BETOXL/P-Keeper/Plans3Dfiles/P-Keeper Plans/lateral de motor - Sheet1.pdf

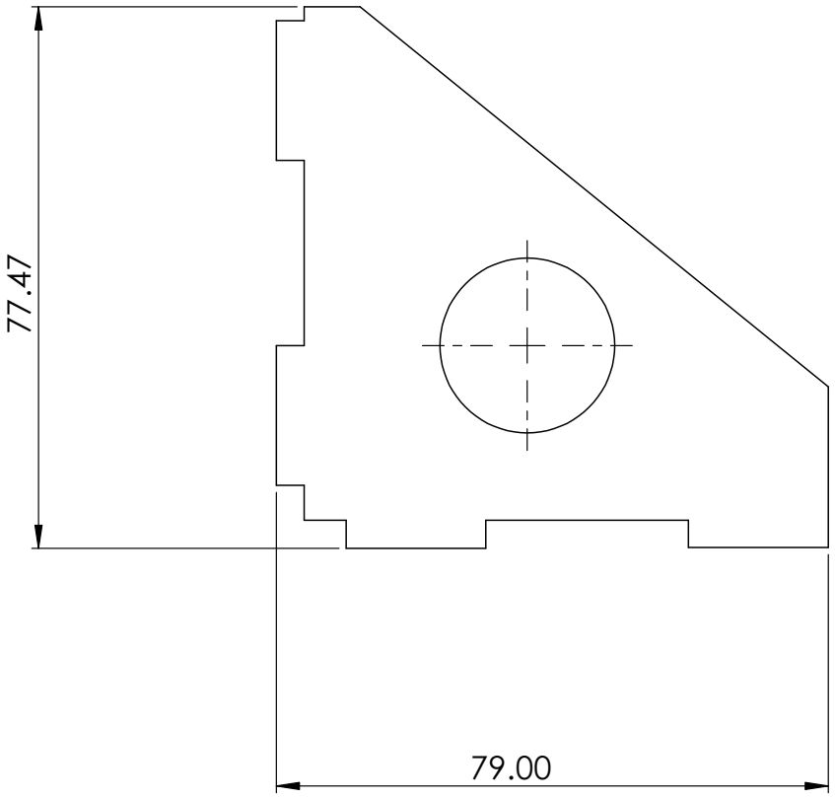
[picture p3: figure]
