BETOXL/P-Keeper/Plans3Dfiles/P-Keeper Plans/soporte de entrepiso - Sheet1.pdf

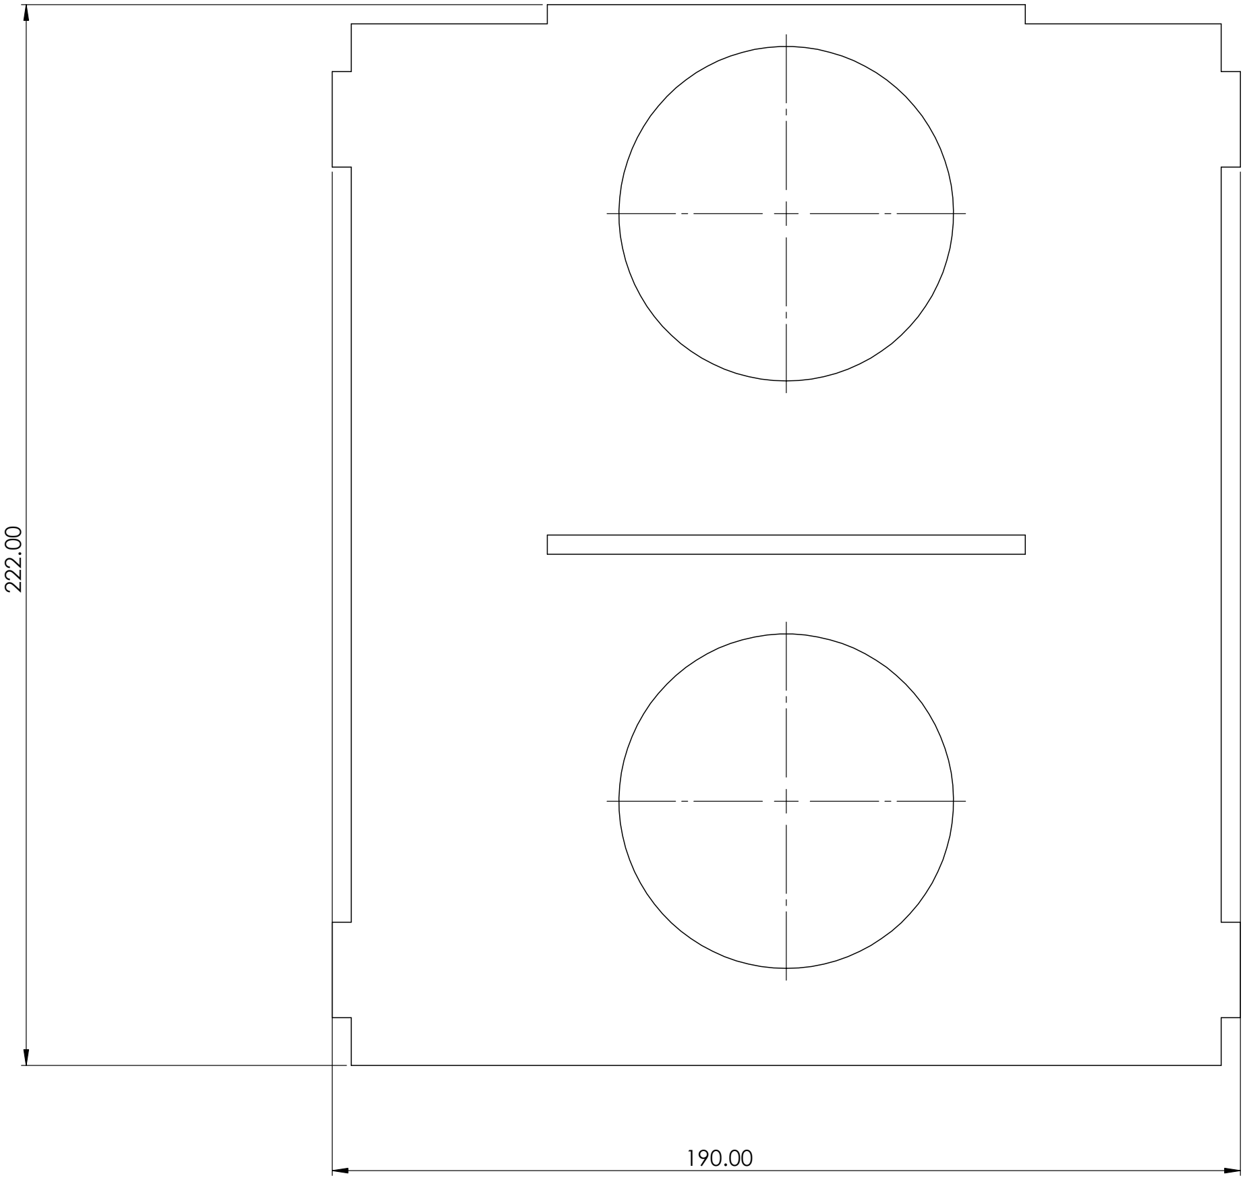
[picture p4: figure]
