BETOXL/P-Keeper/Plans3Dfiles/back.JPG

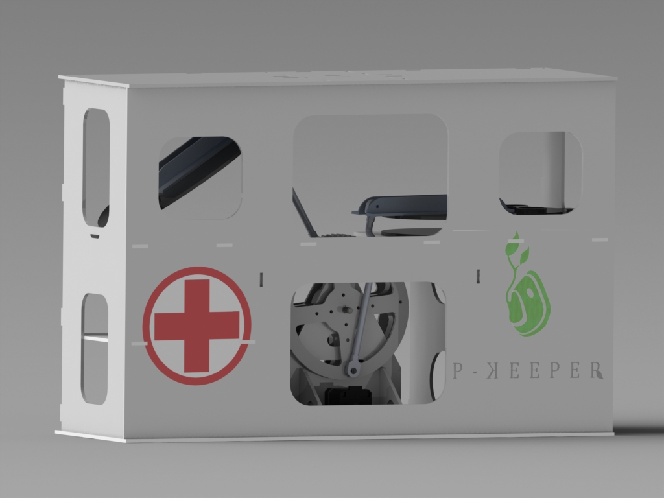
Plans3Dfiles/back.JPG
