BETOXL/P-Keeper/Plans3Dfiles/total assy.SLDASM

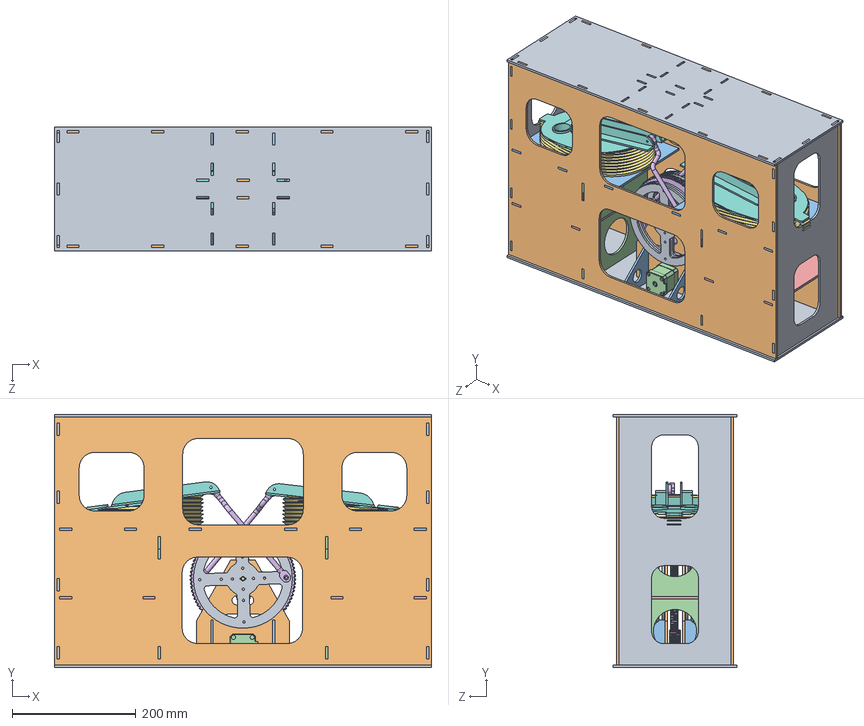
[picture p26: CAD file, 2020-05-05]
Plans3Dfiles/total assy.SLDASM
610.0 x 410.0 x 200.0 mm
piso 2 x 2
frente de motor x 2
lateral de motor x 4
nema 17 x 2
pinon
Corona
eje principal
perno de eje
rueda x 4
lateral x 2
entrepiso x 2
soporte de entrepiso x 2
piso para electronica x 2
bastago x 2
tapa de fuelle2 x 2
tapa sup de fuelle x 2
frentes x 2
