BETOXL/P-Keeper/Plans3Dfiles/Respirator2.SLDASM

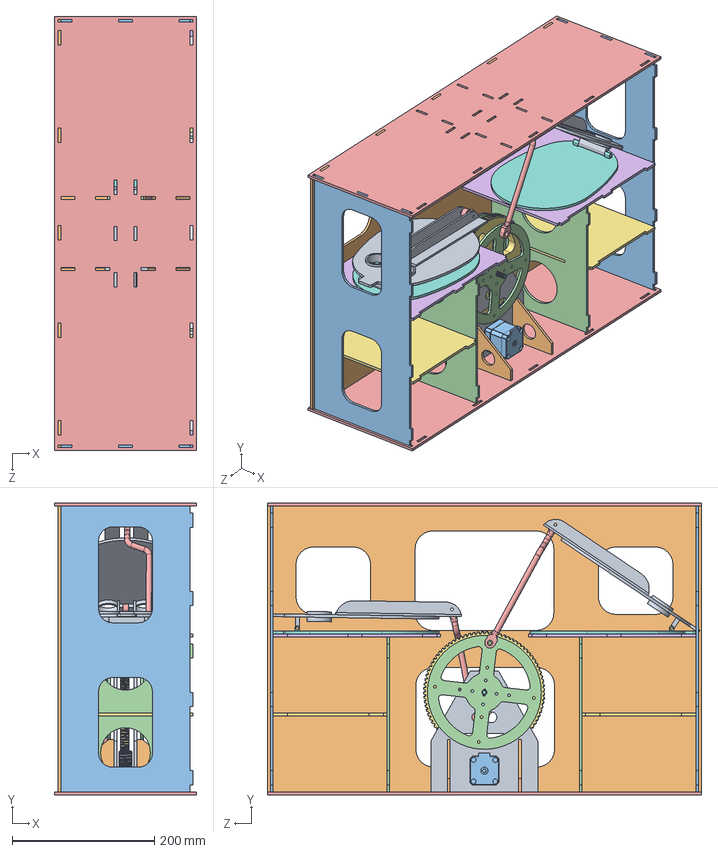
[picture p27: CAD file, 2020-05-05]
Plans3Dfiles/Respirator2.SLDASM
200.0 x 410.0 x 610.0 mm
frente de motor x 2
lateral de motor x 4
nema 17 x 2
rueda x 2
piso 2 x 2
entrepiso x 2
piso para electronica x 2
tapa de fuelle x 2
tapa sup de fuelle x 2
lateral
frentes x 2
soporte de entrepiso x 2
bastago x 2
pinon
Corona
eje principal
perno de eje x 3
