BETOXL/P-Keeper/Plans3Dfiles/main gear 94t.SLDPRT

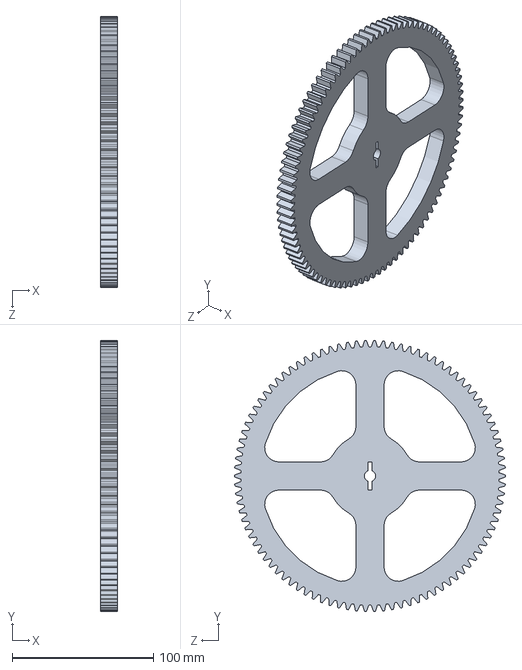
[picture p28: CAD file, 2020-05-05]
Plans3Dfiles/main gear 94t.SLDPRT
12.0 x 191.9 x 192.0 mm
