BETOXL/P-Keeper/Plans3Dfiles/3D files P-Keeper/niple conector de manguera.STL

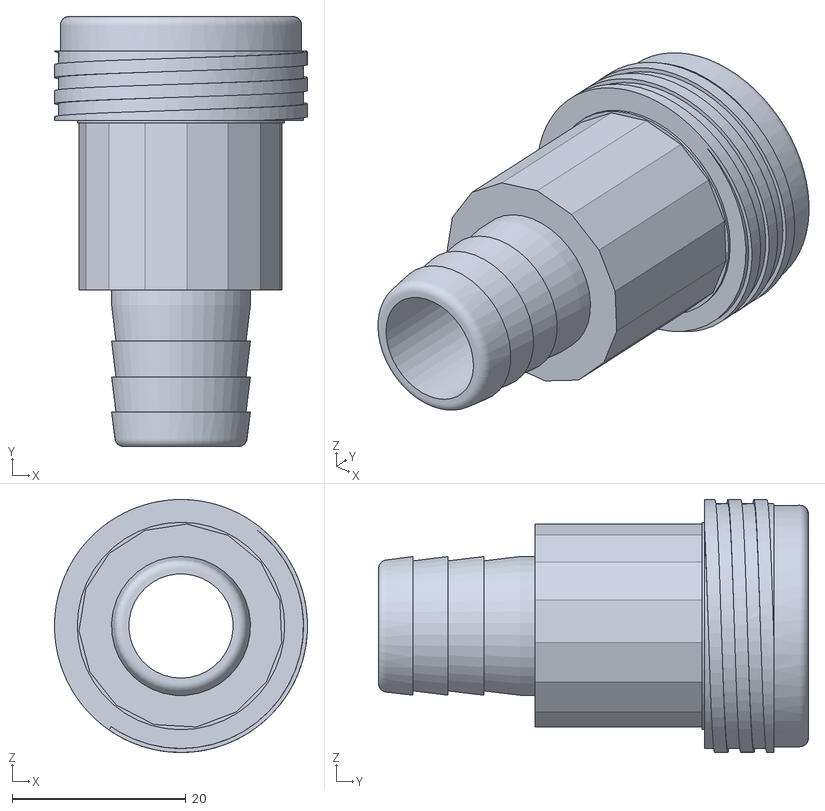
[picture p29: CAD file, 2020-05-05]
Plans3Dfiles/3D files P-Keeper/niple conector de manguera.STL
29.1 x 49.5 x 29.1
