BETOXL/P-Keeper/Plans3Dfiles/tapa sup de fuelle.SLDPRT

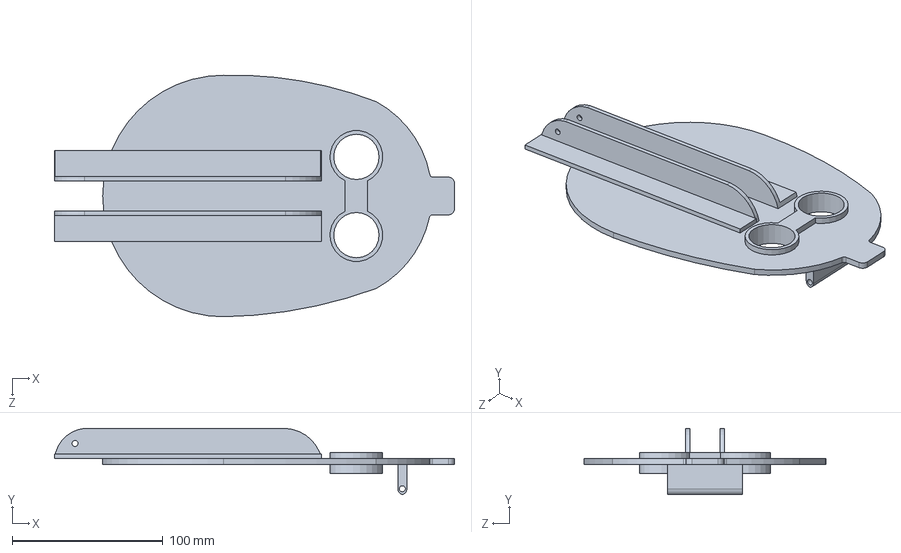
[picture p30: CAD file, 2020-05-05]
Plans3Dfiles/tapa sup de fuelle.SLDPRT
265.0 x 43.9 x 160.0 mm
