BETOXL/P-Keeper/Plans3Dfiles/3D files P-Keeper/tuerca de camara Y.STL

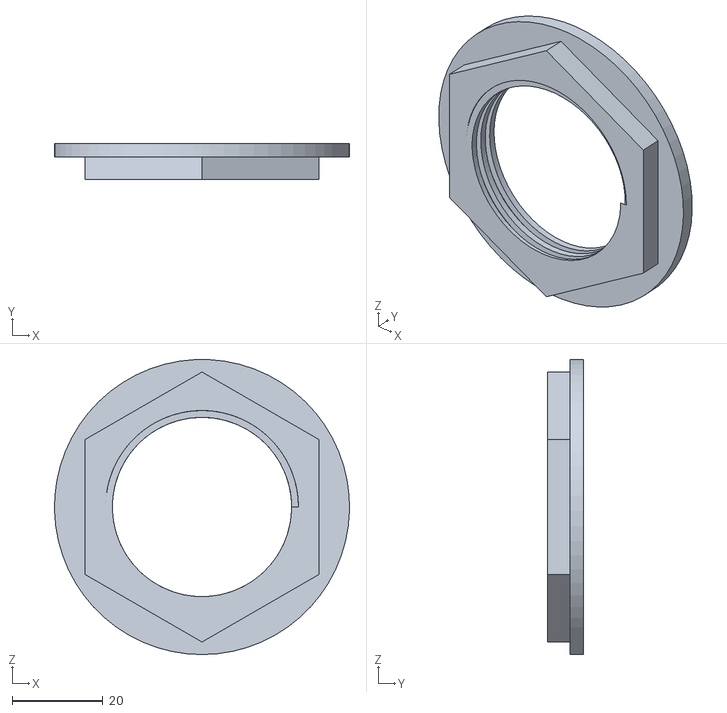
[picture p31: CAD file, 2020-05-05]
Plans3Dfiles/3D files P-Keeper/tuerca de camara Y.STL
65.0 x 8.00 x 65.0
