BETOXL/P-Keeper/Plans3Dfiles/potenciometer top.SLDPRT

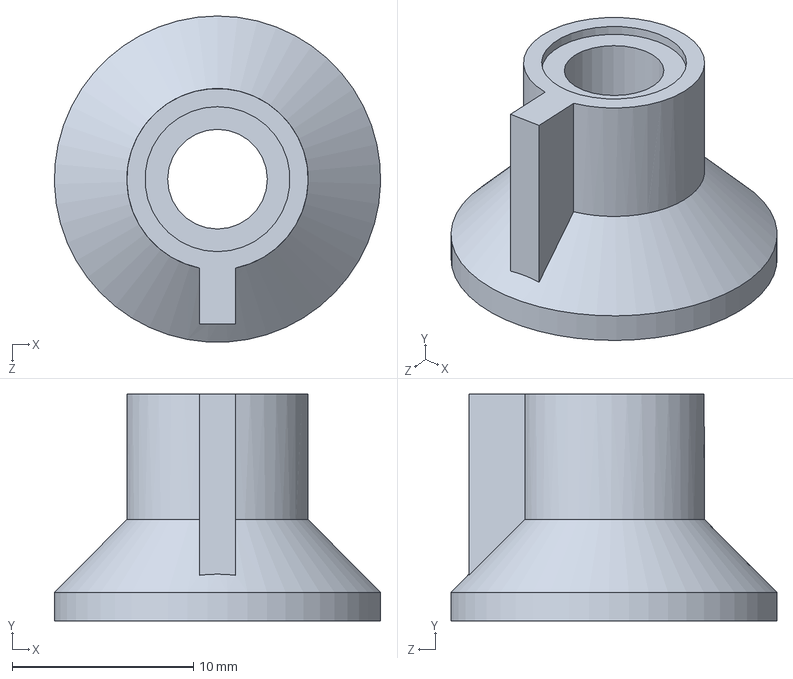
[picture p32: CAD file, 2020-05-05]
Plans3Dfiles/potenciometer top.SLDPRT
18.0 x 12.5 x 18.0 mm
