BETOXL/P-Keeper/Plans3Dfiles/3D files P-Keeper/boquilla con tuerca.STL

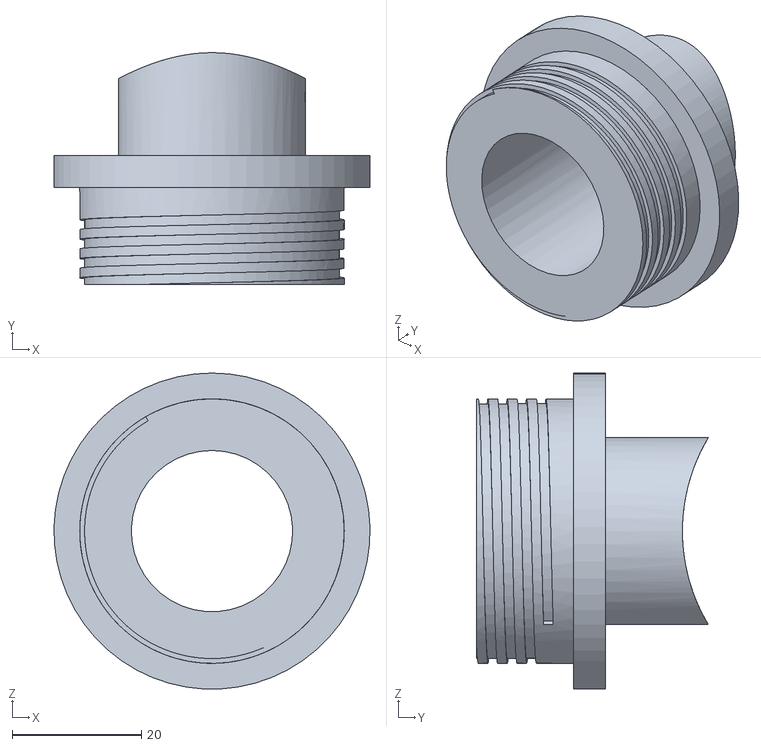
[picture p33: CAD file, 2020-05-05]
Plans3Dfiles/3D files P-Keeper/boquilla con tuerca.STL
49.0 x 35.9 x 49.0
