BETOXL/P-Keeper/Plans3Dfiles/Secondary Gear 3.SLDPRT

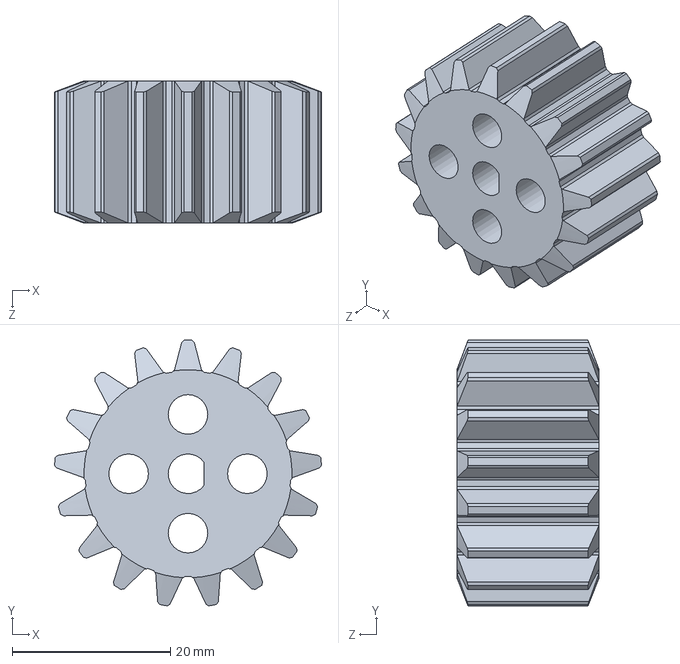
[picture p34: CAD file, 2020-05-05]
Plans3Dfiles/Secondary Gear 3.SLDPRT
33.7 x 33.6 x 18.0 mm
