BETOXL/P-Keeper/Plans3Dfiles/3D files P-Keeper/tapa de camara.STL

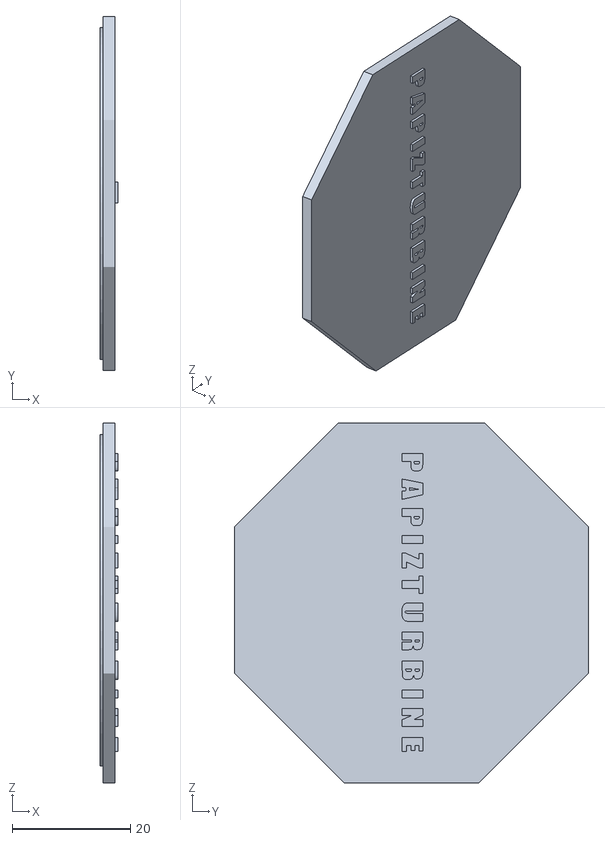
[picture p35: CAD file, 2020-05-05]
Plans3Dfiles/3D files P-Keeper/tapa de camara.STL
3.00 x 60.0 x 61.0
