BETOXL/P-Keeper/Plans3Dfiles/Shaft PIN.SLDPRT

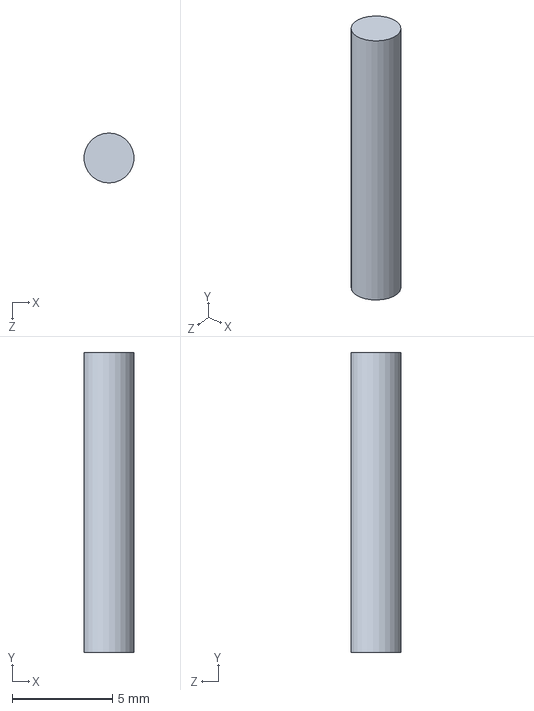
[picture p36: CAD file, 2020-05-05]
Plans3Dfiles/Shaft PIN.SLDPRT
2.48 x 15.0 x 2.50 mm
