BETOXL/P-Keeper/Plans3Dfiles/3D files P-Keeper/conector Y comun.STL

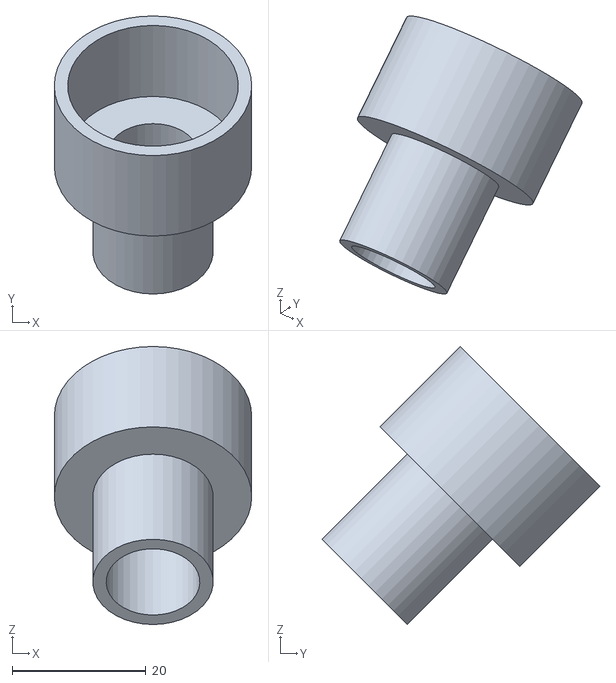
[picture p37: CAD file, 2020-05-05]
Plans3Dfiles/3D files P-Keeper/conector Y comun.STL
29.5 x 41.5 x 41.5
