BETOXL/P-Keeper/Plans3Dfiles/nema 17.SLDPRT

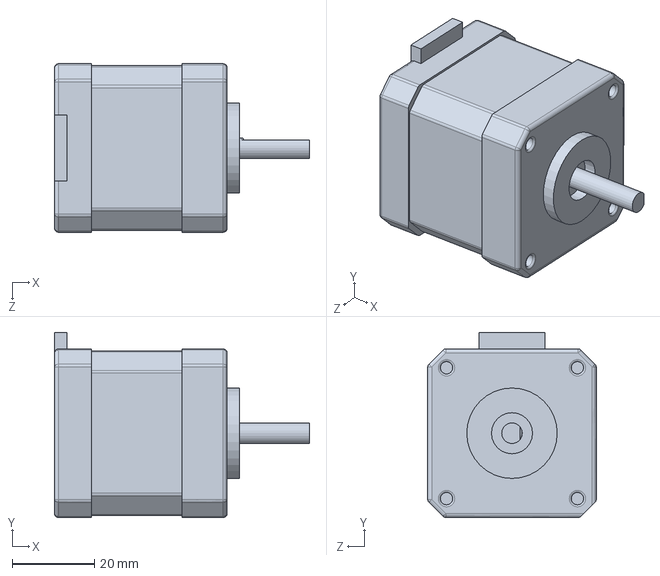
[picture p38: CAD file, 2020-05-05]
Plans3Dfiles/nema 17.SLDPRT
62.0 x 45.0 x 41.0 mm
