BETOXL/P-Keeper/Plans3Dfiles/3D files P-Keeper/cuerpo de Camara Y.STL

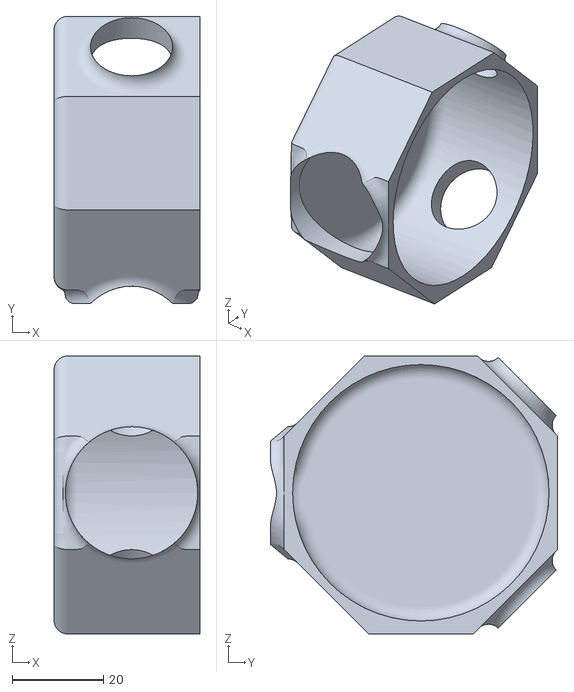
[picture p39: CAD file, 2020-05-05]
Plans3Dfiles/3D files P-Keeper/cuerpo de Camara Y.STL
32.0 x 63.0 x 61.0
