BETOXL/P-Keeper/Plans3Dfiles/Actuator Support.STL

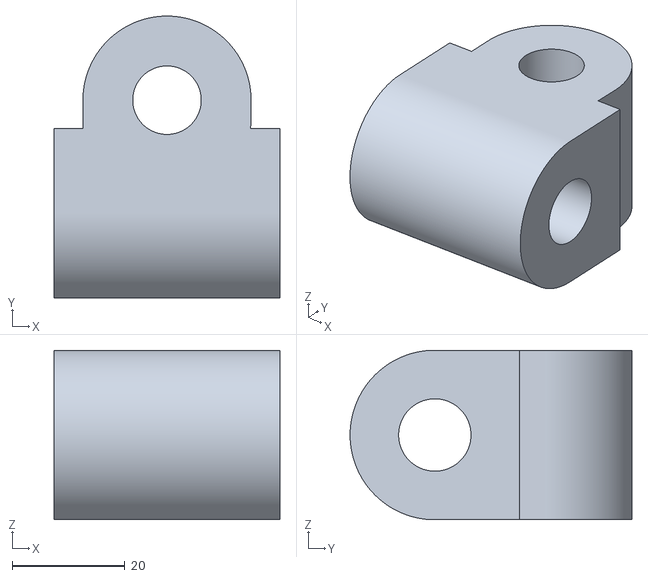
[picture p40: CAD file, 2020-05-05]
Plans3Dfiles/Actuator Support.STL
40.0 x 49.9 x 30.0
