BETOXL/P-Keeper/Plans3Dfiles/crown3.SLDPRT

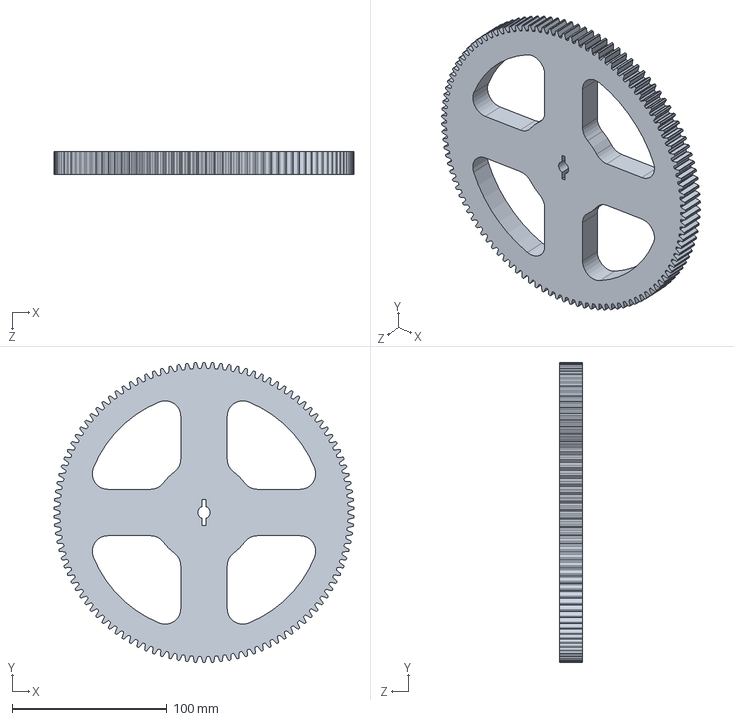
[picture p41: CAD file, 2020-05-05]
Plans3Dfiles/crown3.SLDPRT
193.7 x 193.8 x 15.0 mm
