BETOXL/P-Keeper/Plans3Dfiles/both Shafts distance.SLDPRT

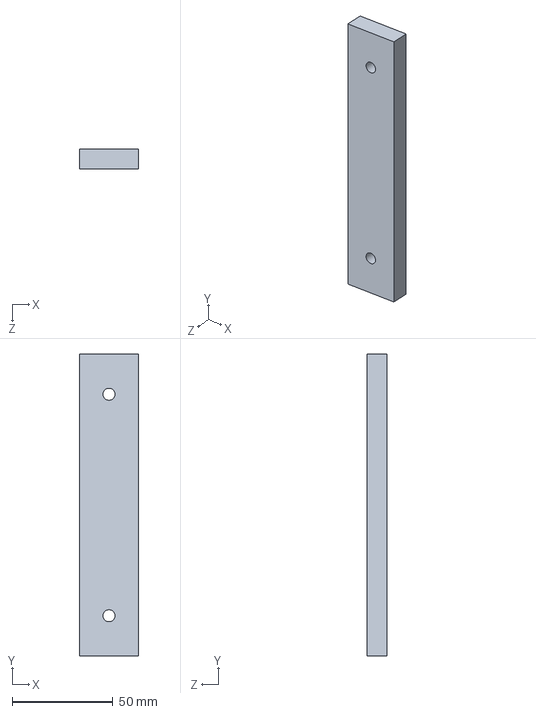
[picture p42: CAD file, 2020-05-05]
Plans3Dfiles/both Shafts distance.SLDPRT
29.2 x 150.0 x 10.0 mm
