BETOXL/P-Keeper/Plans3Dfiles/Secondary Gear.SLDPRT

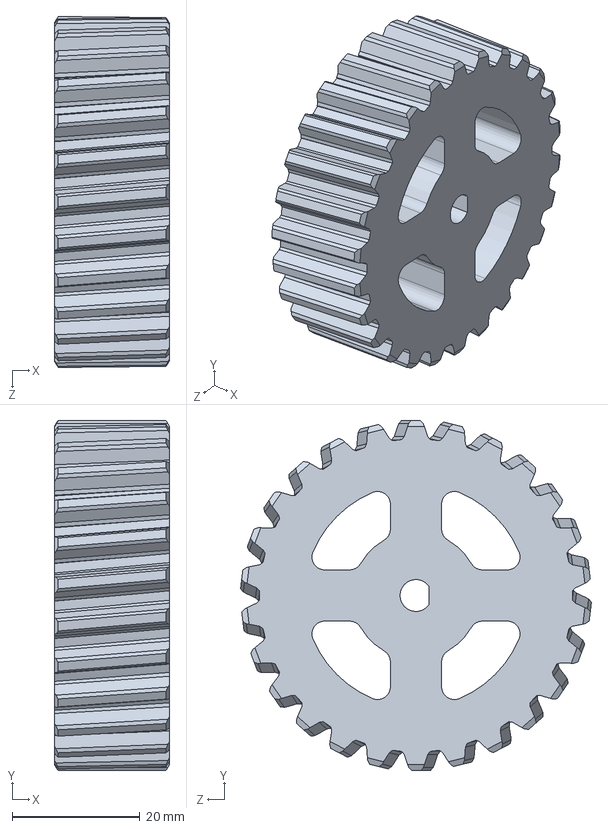
[picture p43: CAD file, 2020-05-05]
Plans3Dfiles/Secondary Gear.SLDPRT
18.0 x 54.8 x 54.9 mm
