BETOXL/P-Keeper/Plans3Dfiles/common conector.SLDPRT

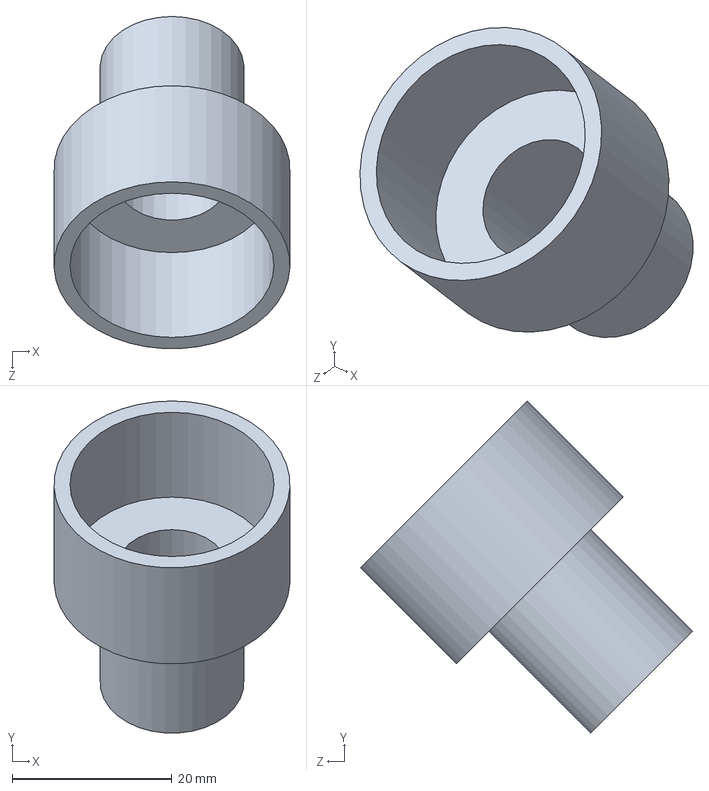
[picture p44: CAD file, 2020-05-05]
Plans3Dfiles/common conector.SLDPRT
29.5 x 41.5 x 41.5 mm
