BETOXL/P-Keeper/Plans3Dfiles/tapa de fuelle.SLDPRT

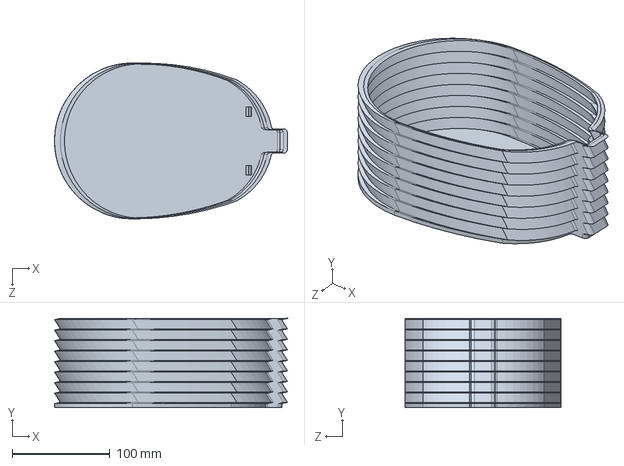
[picture p45: CAD file, 2020-05-05]
Plans3Dfiles/tapa de fuelle.SLDPRT
238.9 x 91.5 x 160.0 mm
