BETOXL/P-Keeper/Plans3Dfiles/crown 2.SLDPRT

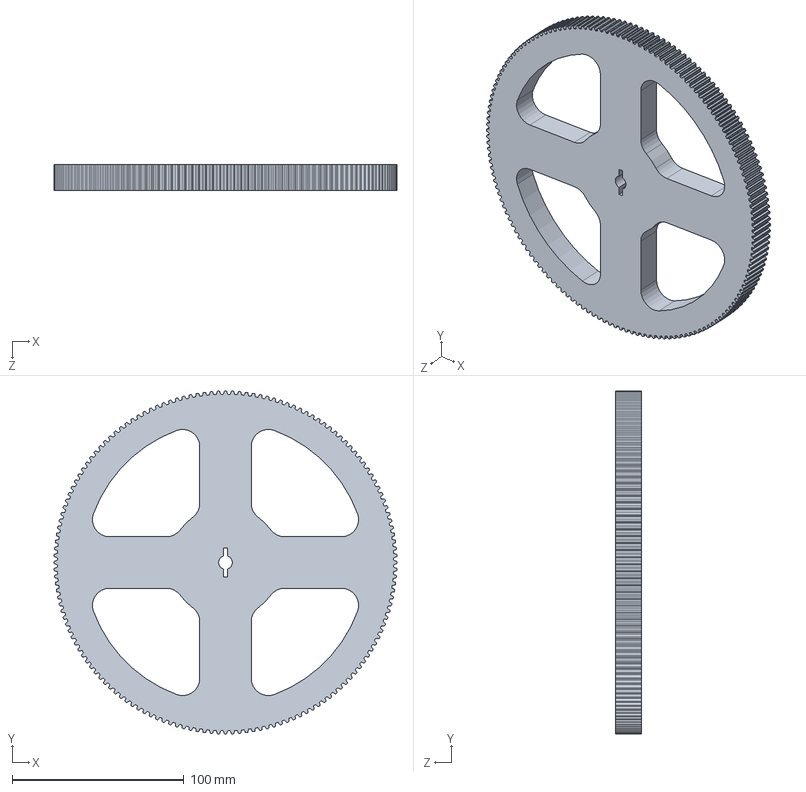
[picture p46: CAD file, 2020-05-05]
Plans3Dfiles/crown 2.SLDPRT
199.8 x 199.8 x 15.0 mm
