BETOXL/P-Keeper/Plans3Dfiles/Floor 1.SLDPRT

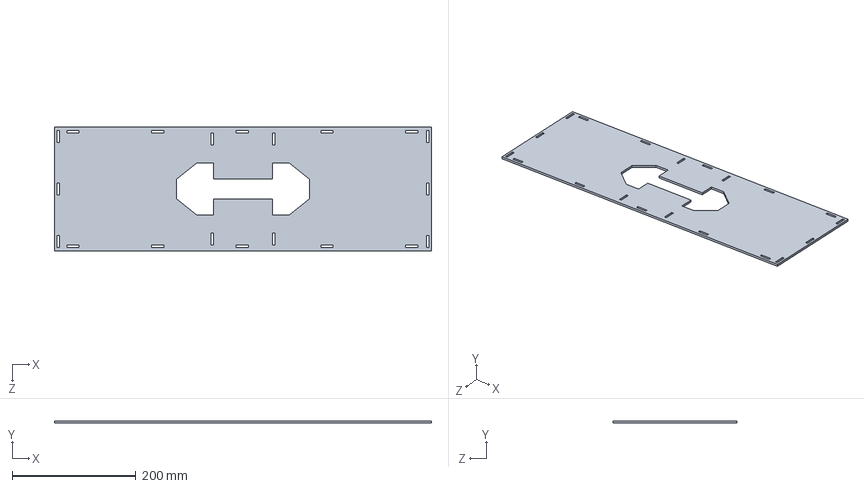
[picture p47: CAD file, 2020-05-05]
Plans3Dfiles/Floor 1.SLDPRT
610.0 x 4.00 x 200.0 mm
