BETOXL/P-Keeper/Plans3Dfiles/screen suport.SLDPRT

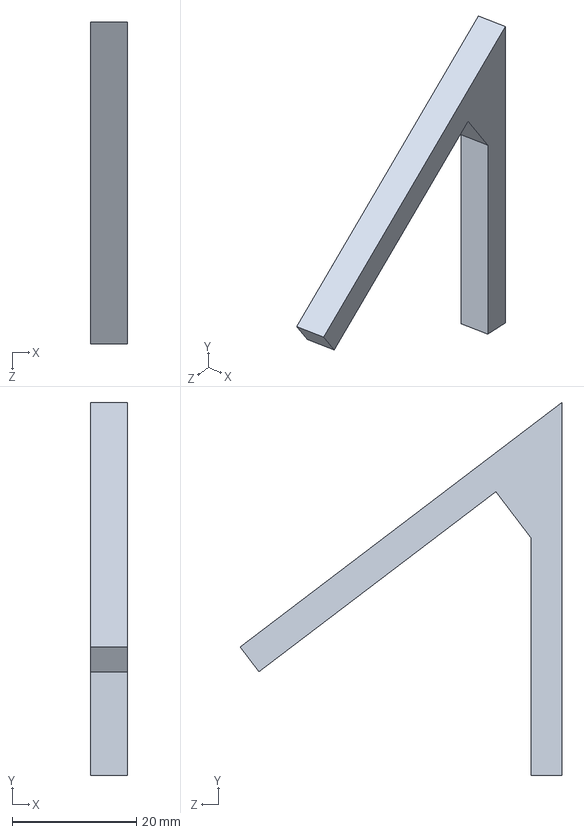
[picture p48: CAD file, 2020-05-05]
Plans3Dfiles/screen suport.SLDPRT
6.00 x 60.0 x 51.8 mm
