BETOXL/P-Keeper/Plans3Dfiles/y Chamber.SLDPRT

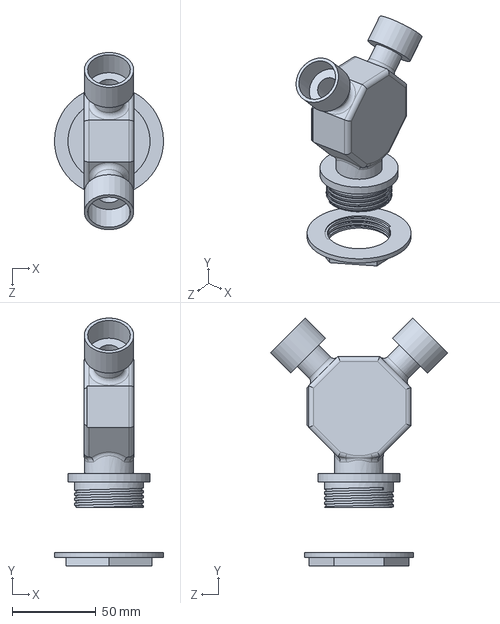
[picture p49: CAD file, 2020-05-05]
Plans3Dfiles/y Chamber.SLDPRT
65.0 x 147.9 x 105.6 mm
