BETOXL/P-Keeper/Plans3Dfiles/Actuator Wheel.SLDPRT

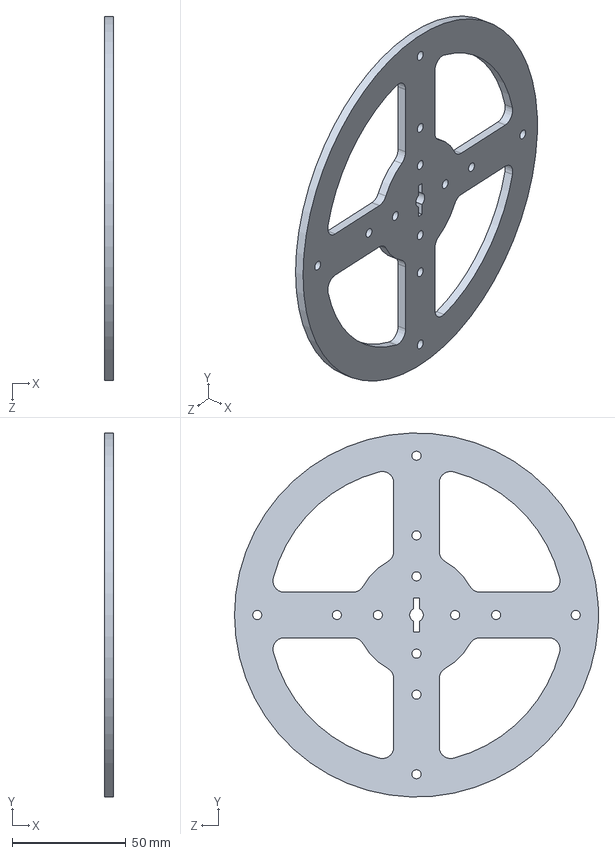
[picture p50: CAD file, 2020-05-05]
Plans3Dfiles/Actuator Wheel.SLDPRT
4.00 x 159.9 x 160.0 mm
