BETOXL/P-Keeper/Plans3Dfiles/Front and Back Wall.SLDPRT

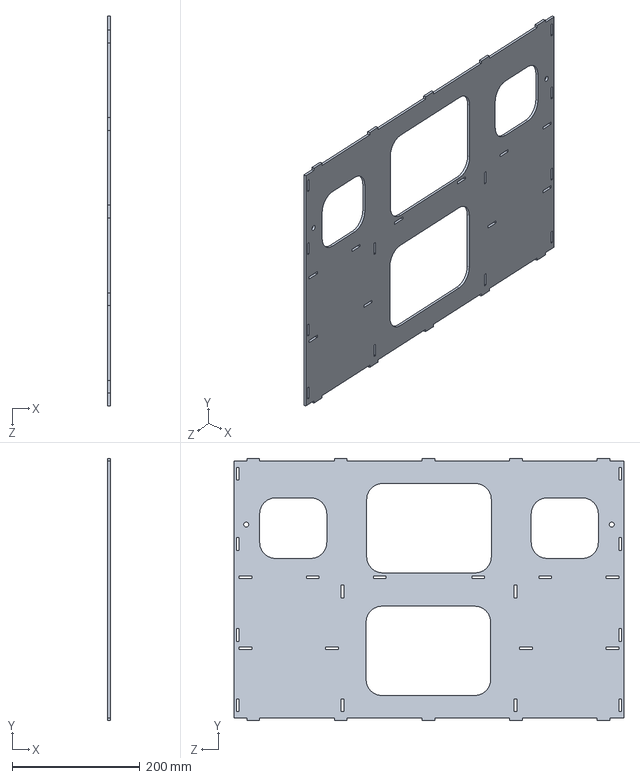
[picture p51: CAD file, 2020-05-05]
Plans3Dfiles/Front and Back Wall.SLDPRT
4.00 x 410.0 x 610.0 mm
