BETOXL/P-Keeper/Plans3Dfiles/clevis.SLDPRT

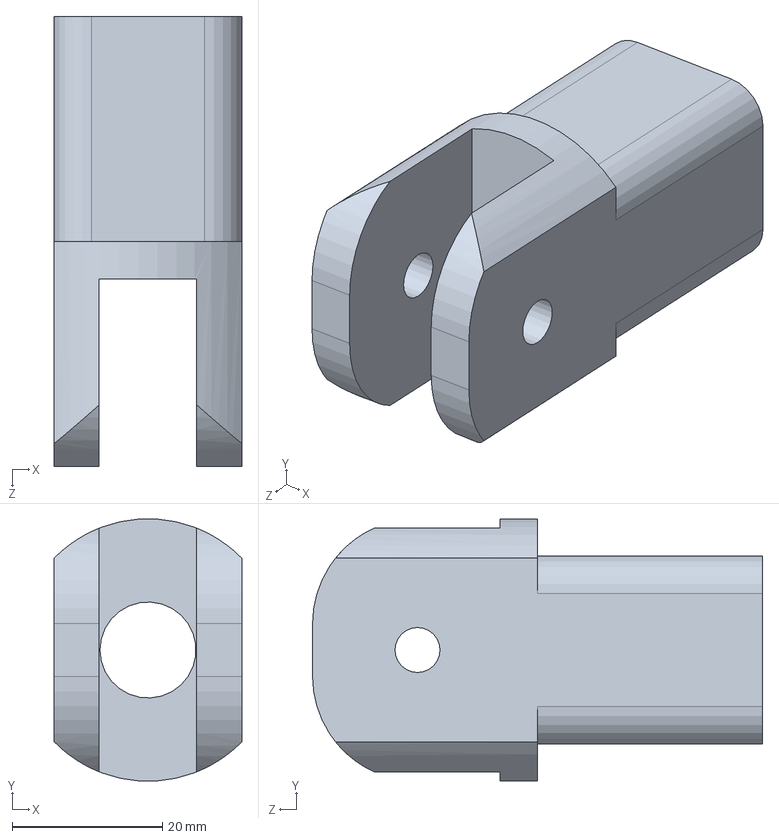
[picture p52: CAD file, 2020-05-05]
Plans3Dfiles/clevis.SLDPRT
25.0 x 34.9 x 60.0 mm
