BETOXL/P-Keeper/Plans3Dfiles/Sides.SLDPRT

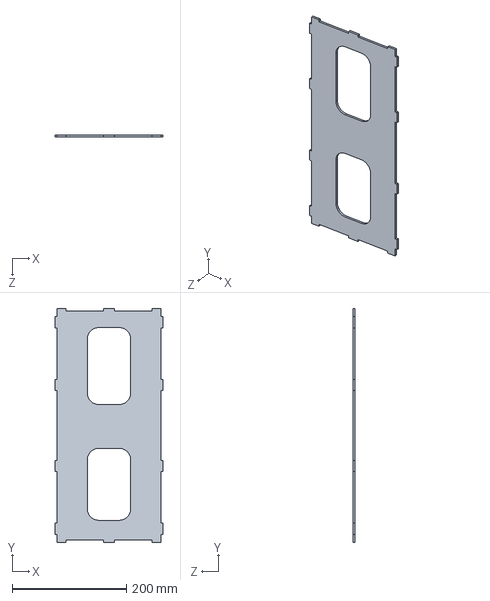
[picture p53: CAD file, 2020-05-05]
Plans3Dfiles/Sides.SLDPRT
190.0 x 410.0 x 4.00 mm
