BETOXL/P-Keeper/Plans3Dfiles/Electronic's Floor.SLDPRT

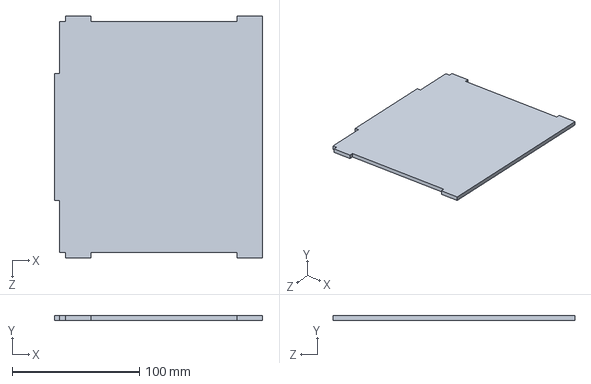
[picture p54: CAD file, 2020-05-05]
Plans3Dfiles/Electronic's Floor.SLDPRT
163.6 x 4.00 x 190.0 mm
