BETOXL/P-Keeper/Plans3Dfiles/actuator tube.SLDPRT

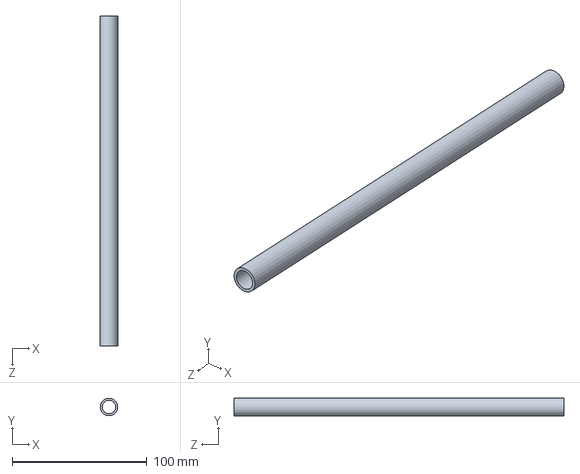
[picture p55: CAD file, 2020-05-05]
Plans3Dfiles/actuator tube.SLDPRT
13.0 x 13.0 x 245.0 mm
