BETOXL/P-Keeper/Plans3Dfiles/Actuator Rod.SLDPRT

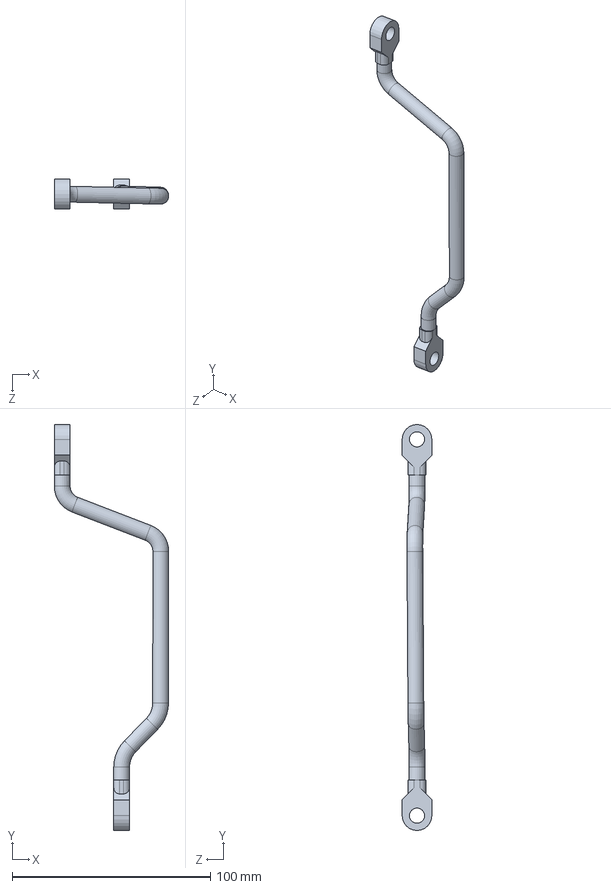
[picture p56: CAD file, 2020-05-05]
Plans3Dfiles/Actuator Rod.SLDPRT
57.8 x 205.0 x 15.0 mm
