BETOXL/P-Keeper/Plans3Dfiles/Middle Floor.SLDPRT

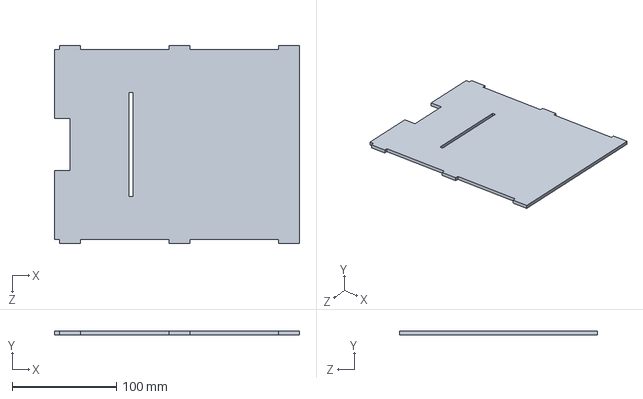
[picture p57: CAD file, 2020-05-05]
Plans3Dfiles/Middle Floor.SLDPRT
235.0 x 4.00 x 190.0 mm
