BETOXL/P-Keeper/Plans3Dfiles/Floor 2.SLDPRT

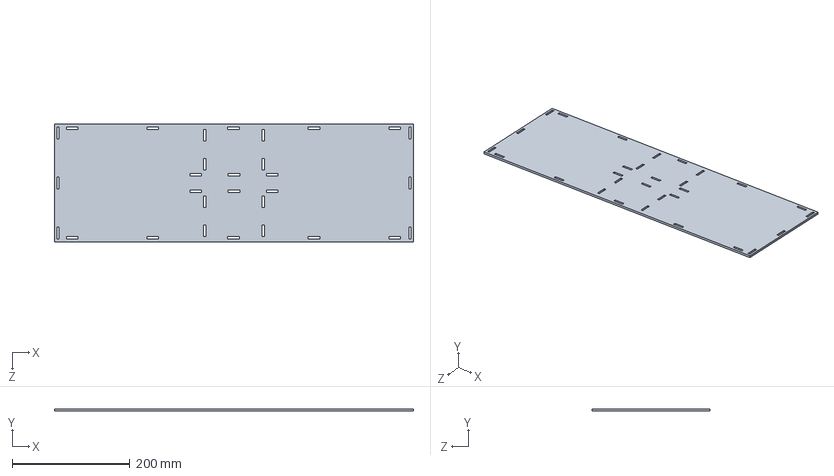
[picture p58: CAD file, 2020-05-05]
Plans3Dfiles/Floor 2.SLDPRT
610.0 x 4.00 x 200.0 mm
