BETOXL/P-Keeper/Plans3Dfiles/tapa de fuelle2.SLDPRT

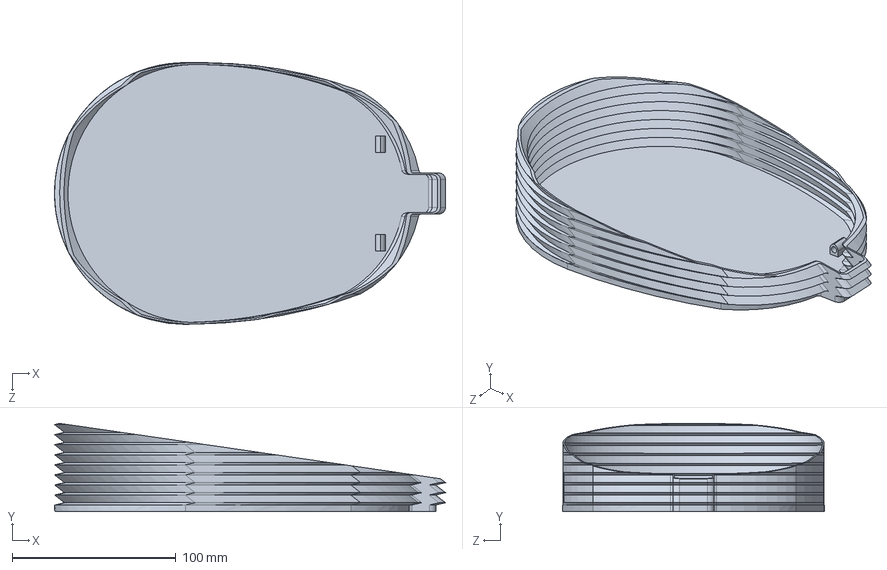
[picture p59: CAD file, 2020-05-05]
Plans3Dfiles/tapa de fuelle2.SLDPRT
238.9 x 53.9 x 160.0 mm
