BETOXL/P-Keeper/Plans3Dfiles/secondary gear 10t.SLDPRT

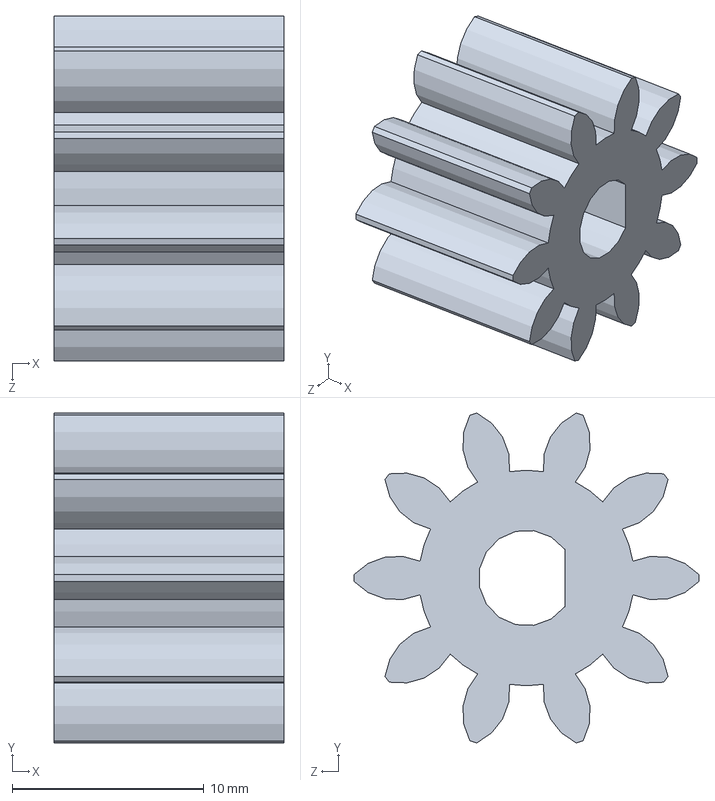
[picture p60: CAD file, 2020-05-05]
Plans3Dfiles/secondary gear 10t.SLDPRT
12.0 x 17.2 x 18.0 mm
