BETOXL/P-Keeper/Plans3Dfiles/Floor.SLDPRT

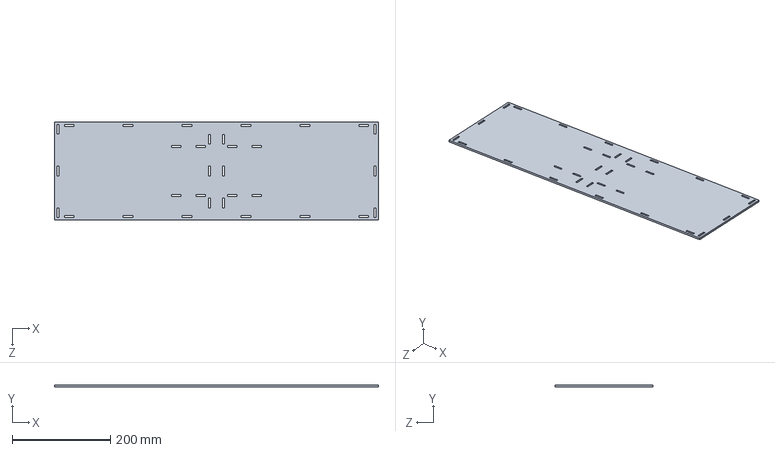
[picture p61: CAD file, 2020-05-05]
Plans3Dfiles/Floor.SLDPRT
660.0 x 4.00 x 200.0 mm
