BETOXL/P-Keeper/Plans3Dfiles/Motor Front Wall.SLDPRT

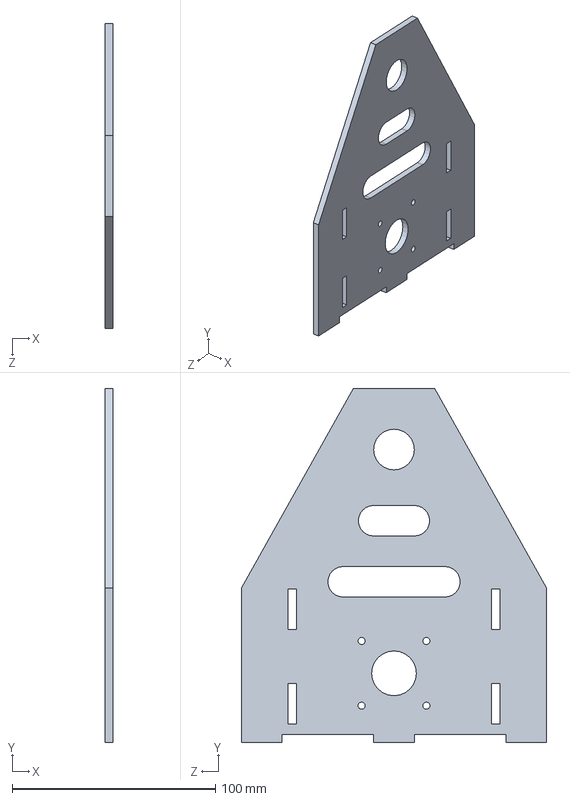
[picture p62: CAD file, 2020-05-05]
Plans3Dfiles/Motor Front Wall.SLDPRT
4.00 x 174.0 x 150.0 mm
