BETOXL/P-Keeper/Plans3Dfiles/support actuator tube.SLDPRT

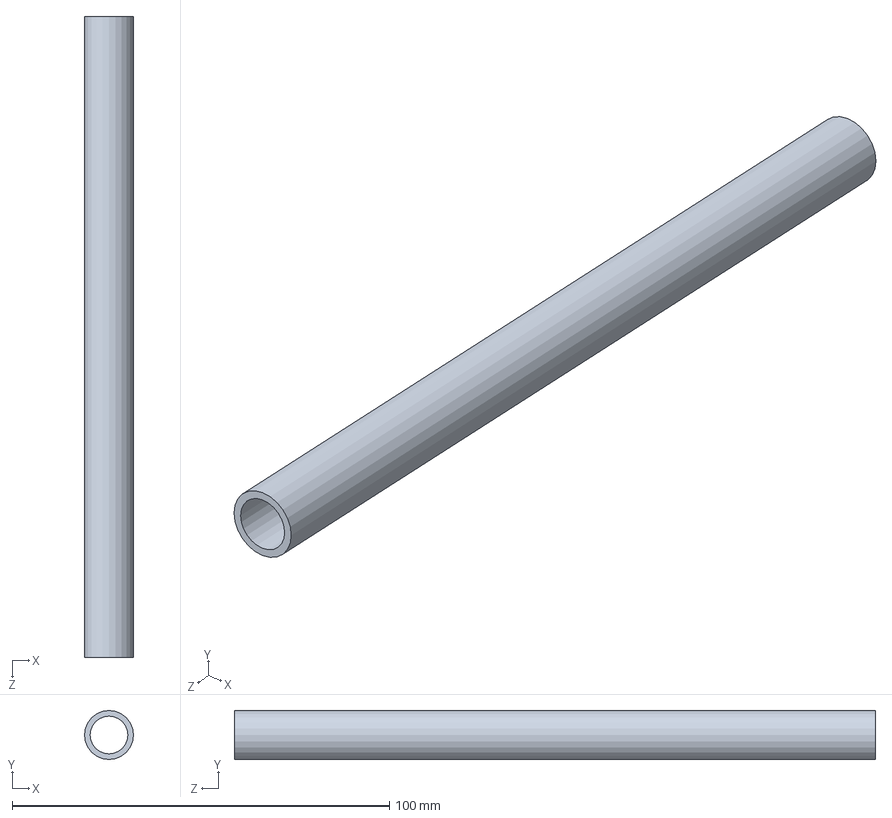
[picture p63: CAD file, 2020-05-05]
Plans3Dfiles/support actuator tube.SLDPRT
13.0 x 13.0 x 170.0 mm
