BETOXL/P-Keeper/Plans3Dfiles/crown.SLDPRT

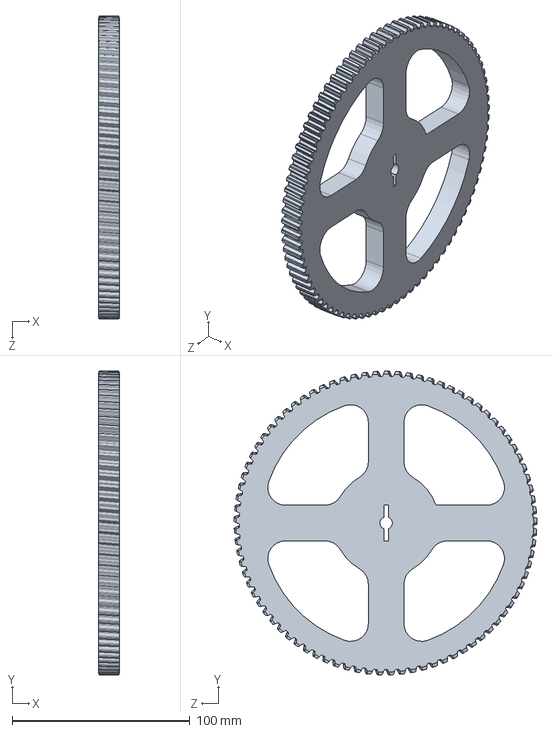
[picture p64: CAD file, 2020-05-05]
Plans3Dfiles/crown.SLDPRT
12.0 x 171.0 x 170.3 mm
