BETOXL/P-Keeper/Plans3Dfiles/Side2.SLDPRT

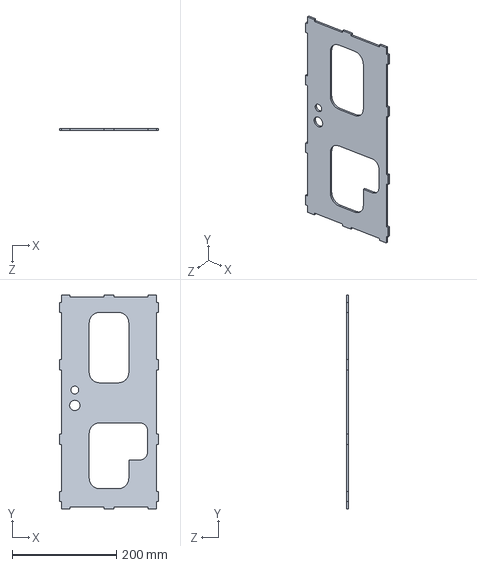
[picture p65: CAD file, 2020-05-05]
Plans3Dfiles/Side2.SLDPRT
190.0 x 410.0 x 4.00 mm
