BETOXL/P-Keeper/Plans3Dfiles/Motor Side Wall.SLDPRT

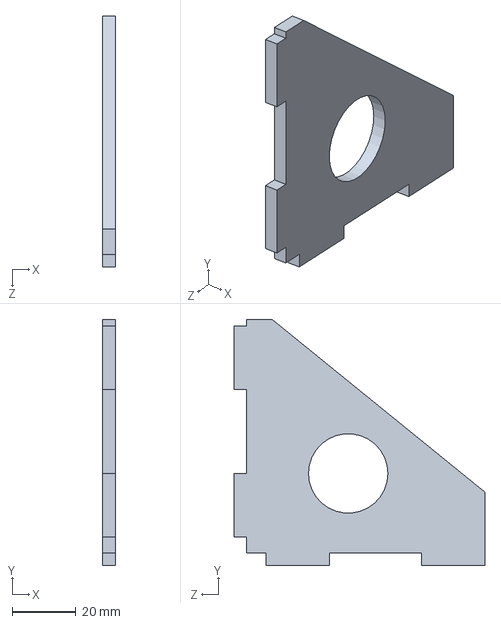
[picture p66: CAD file, 2020-05-05]
Plans3Dfiles/Motor Side Wall.SLDPRT
4.00 x 77.5 x 79.0 mm
