BETOXL/P-Keeper/Plans3Dfiles/bearing DIN 625 - 627 - 8,DE,NC,8_68.SLDPRT

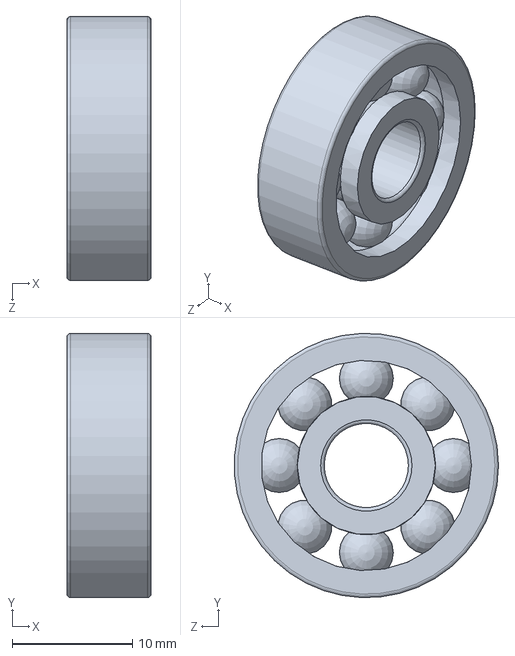
[picture p67: CAD file, 2020-05-05]
Plans3Dfiles/bearing DIN 625 - 627 - 8,DE,NC,8_68.SLDPRT
7.00 x 22.0 x 22.0 mm
