BETOXL/P-Keeper/Plans3Dfiles/MIddle Floor Support.SLDPRT

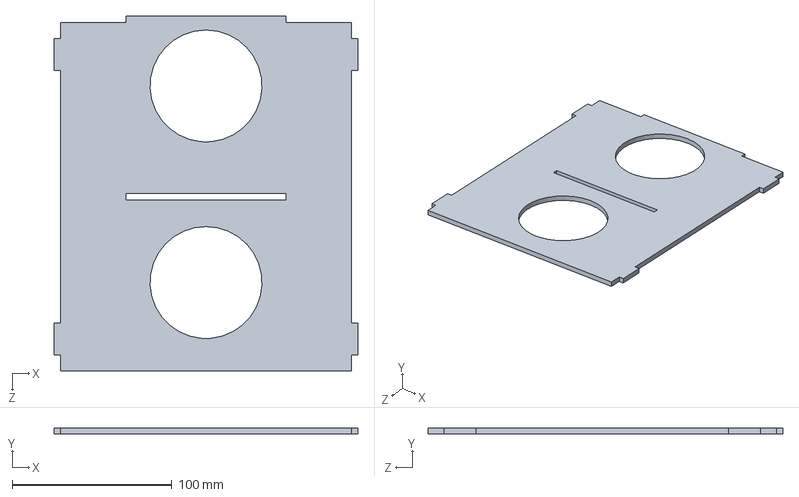
[picture p68: CAD file, 2020-05-05]
Plans3Dfiles/MIddle Floor Support.SLDPRT
190.0 x 4.00 x 222.0 mm
