BETOXL/P-Keeper/Plans3Dfiles/secondary gear 16t.SLDPRT

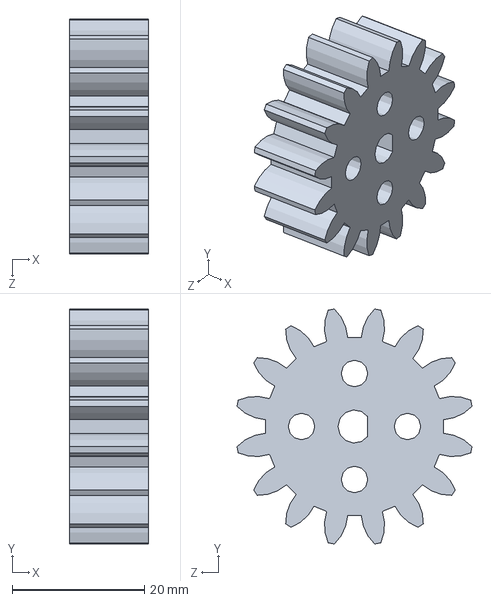
[picture p69: CAD file, 2020-05-05]
Plans3Dfiles/secondary gear 16t.SLDPRT
12.0 x 35.5 x 35.5 mm
