BETOXL/P-Keeper/Plans3Dfiles/pinon3.STEP

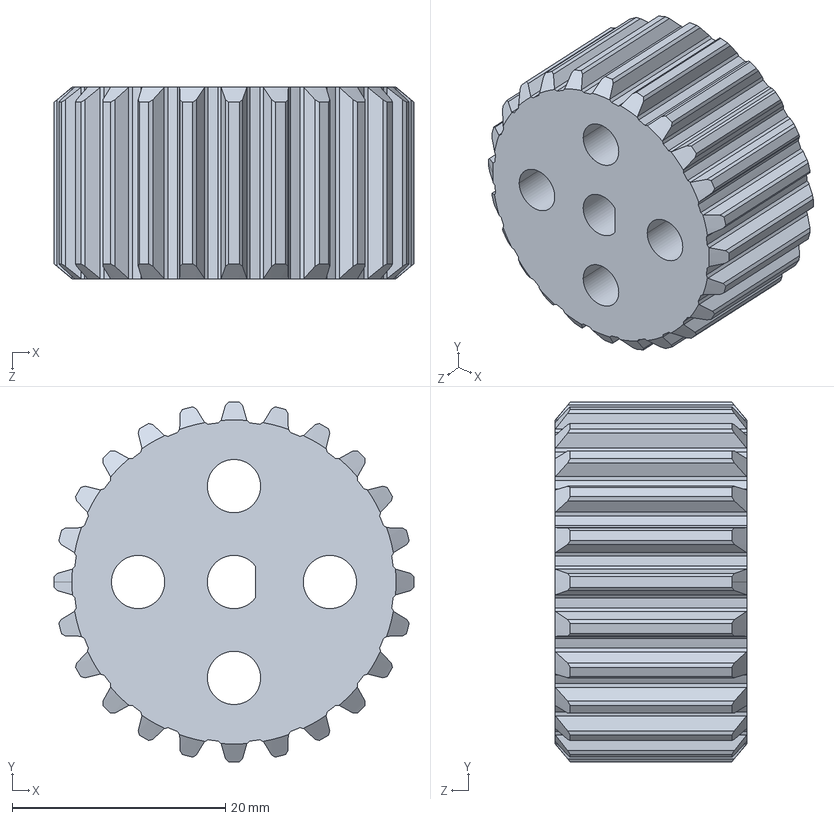
[picture p70: CAD file, 2020-05-05]
Plans3Dfiles/pinon3.STEP
33.8 x 33.8 x 18.0 mm
