BETOXL/P-Keeper/Plans3Dfiles/display front.SLDPRT

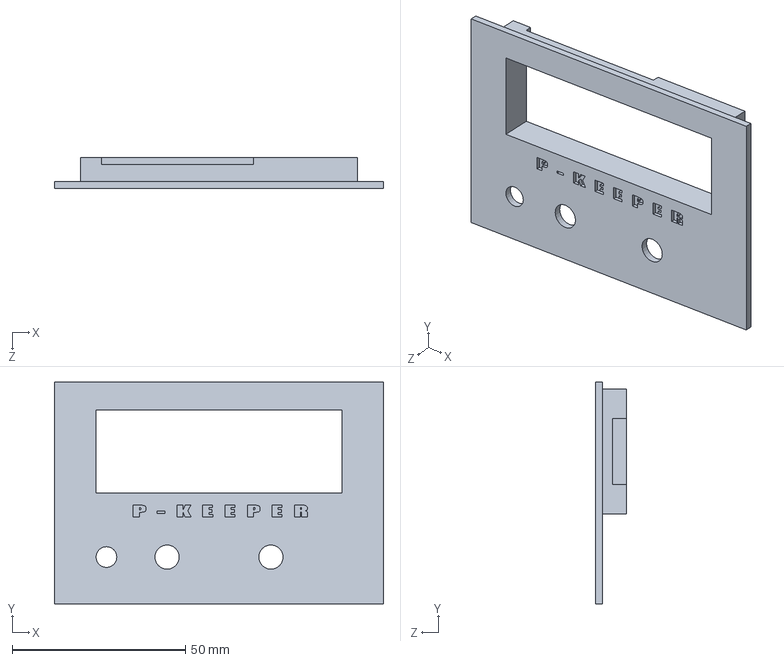
[picture p71: CAD file, 2020-05-05]
Plans3Dfiles/display front.SLDPRT
95.0 x 64.0 x 9.00 mm
