BETOXL/P-Keeper/Plans3Dfiles/Secondary Gear2.SLDPRT

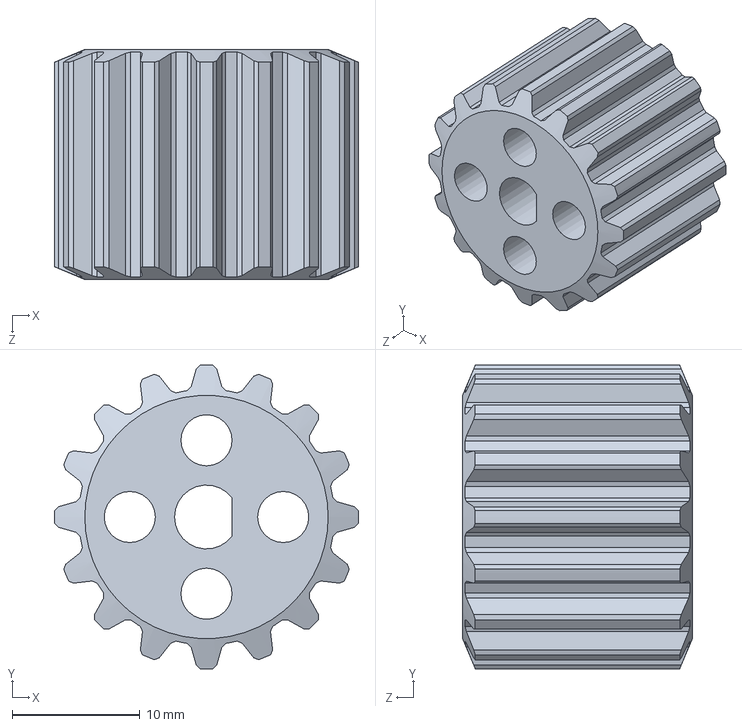
[picture p72: CAD file, 2020-05-05]
Plans3Dfiles/Secondary Gear2.SLDPRT
23.8 x 23.8 x 18.0 mm
